antonloof/eta_game_system/r2r för dac.asc

3.6k: res
R1: res; 1.8k
R2: res; 3.6k
R3: res; 1.8k
R4: res; 3.6k
R5: res; 1.8k
R6: res; 3.6k
R7: res; 1.8k
R8: res; 3.6k
R9: res; 1.8k
R10: res; 1.8k
V1: voltage; PULSE(0 3.3 0 1n 1n 1m 2m)
V2: voltage; PULSE(0 3.3 0 1n 1n 2m 4m)
V3: voltage; PULSE(0 3.3 0 1n 1n 4m 8m)
V4: voltage; PULSE(0 3.3 0 1n 1n 8m 16m)
V5: voltage; PULSE(0 3.3 0 1n 1n 16m 32m)
Named nets: 0
.tran 32m
