antonloof/eta_game_system/tls3001.h

#pragma once

#include "pico/stdlib.h"
#include "hardware/pio.h"
#include "hardware/dma.h"
#include "hardware/irq.h"
#include "manchester.pio.h"

typedef struct tls3001_pixel
{
    uint rg;
    uint b;
} tls3001_pixel;

void init_tls3001(uint pin, PIO pio, uint _pixel_count);
void set_rgb(uint pix, uint r, uint g, uint b);
void swap_buffers();
