antonloof/eta_game_system/pico_test.c

#include "pico/stdlib.h"
#include "hardware/pio.h"
#include "hardware/clocks.h"
#include "hardware/gpio.h"

#include "tls3001.h"
#include "matrix_with_extra.h"
#include "matrices.h"
#include "tetris.h"
#include "scoreboard.h"

#include "hardware/adc.h"
#include "controller.h"

#define TLS_PIN 22
#define TLS_PIO pio0

#define SCOREBOARD_PIN 2
#define SCOREBOARD_PIO pio1

void init_rng();
void player_zero_action(uint8_t);

uint game_over = 1;

int main()
{
    init_rng();
    scoreboard_init(SCOREBOARD_PIN, SCOREBOARD_PIO);
    controller_init(player_zero_action, &player0);

    init_tls3001(TLS_PIN, TLS_PIO, TOTAL_LED_COUNT);
    init_all_matrices();

    while (1)
    {
        while (!game_over)
        {
            game_over = tetris_update();
        }
    }
    return 0;
}

void init_rng()
{
    adc_init();
    adc_select_input(4);
    srand(adc_read());
    // run some random numbers to make numbers less corralated to seed
    for (int i = 0; i < 100; i++)
    {
        rand();
    }
}

void player_zero_action(uint8_t state)
{
    if (game_over)
    {
        game_over = 0;
        scoreboard_set_score(0, 0);
        tetris_init();
    }
    else
    {
        tetris_button_action(state);
    }
}
